diydiagnostics/Photo-Float-Racks/8 Capacity Designs/8C - Backdrop.stl

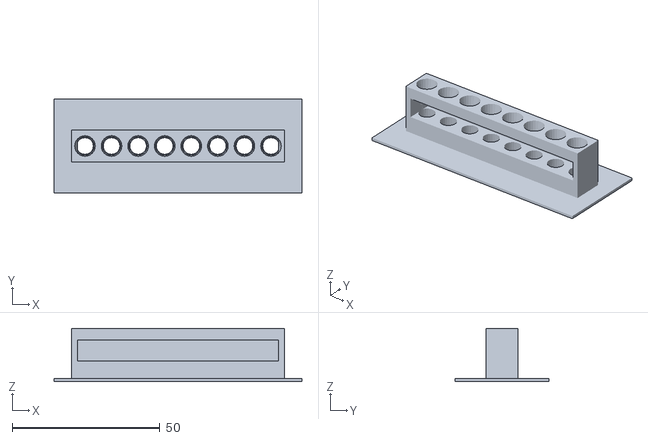
[picture p15: CAD file, 2019-07-22]
8 Capacity Designs/8C - Backdrop.stl
84.0 x 32.0 x 18.0
